MasqueCZ/LuxMeter/blueprints/0.96 I2C display.jpg

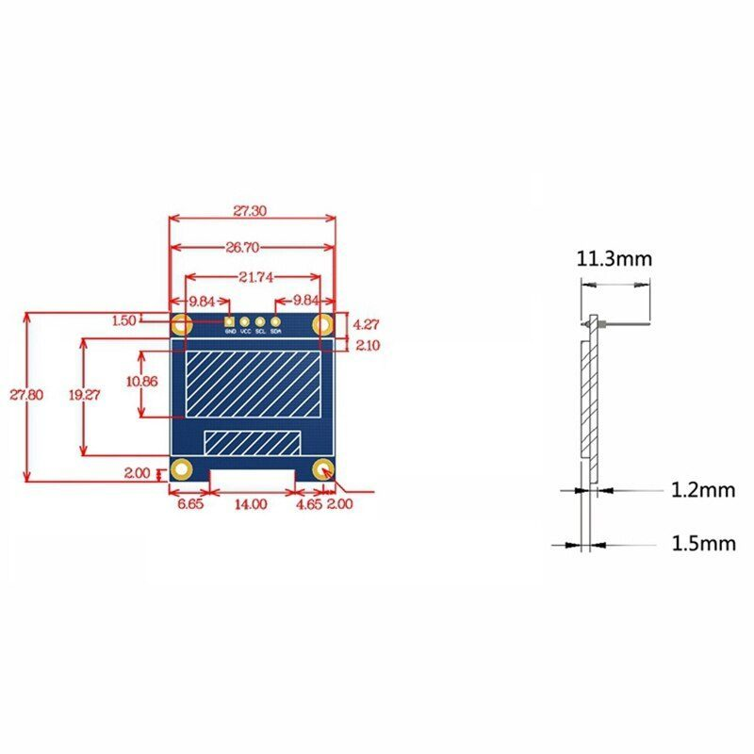
blueprints/0.96 I2C display.jpg
