MasqueCZ/LuxMeter/blueprints/1.54 SPI DISPLAY.jpg

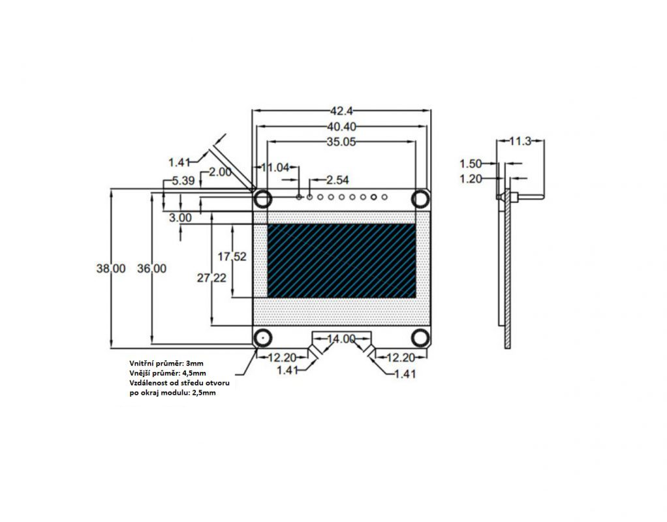
blueprints/1.54 SPI DISPLAY.jpg
