MasqueCZ/LuxMeter/blueprints/CORRIDOR BOX scheme.png

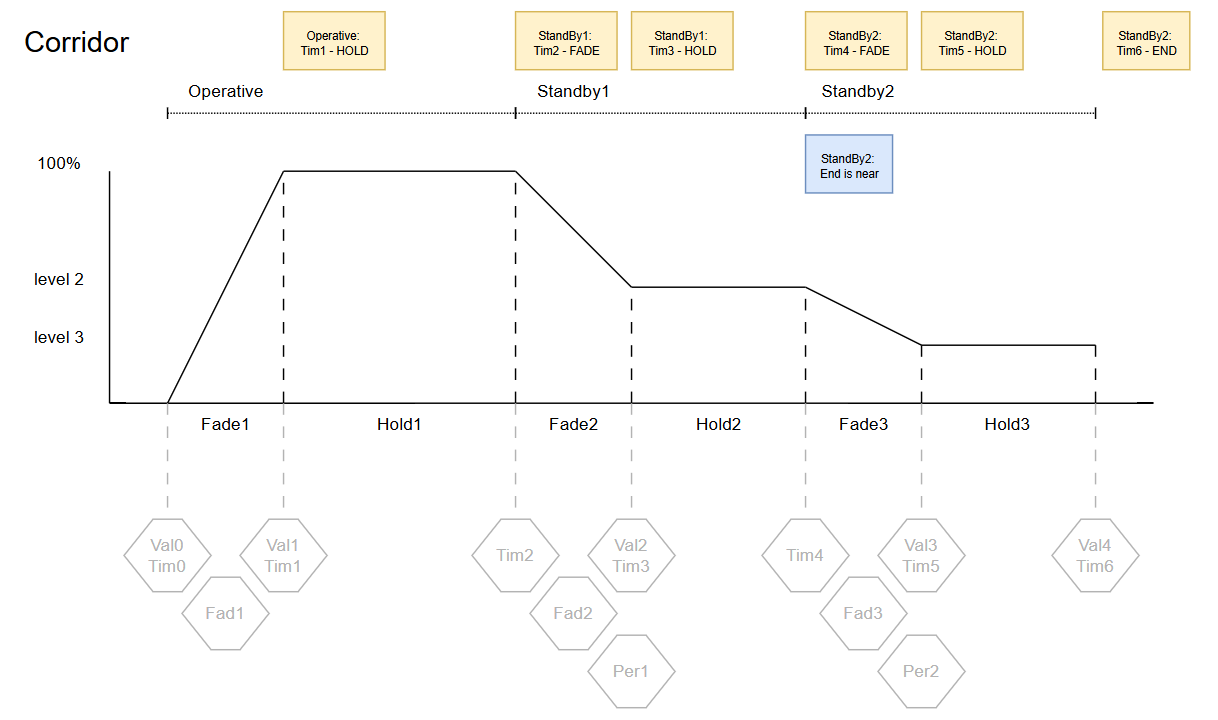
blueprints/CORRIDOR BOX scheme.png
