MasqueCZ/LuxMeter/blueprints/corridor scheme 03.png

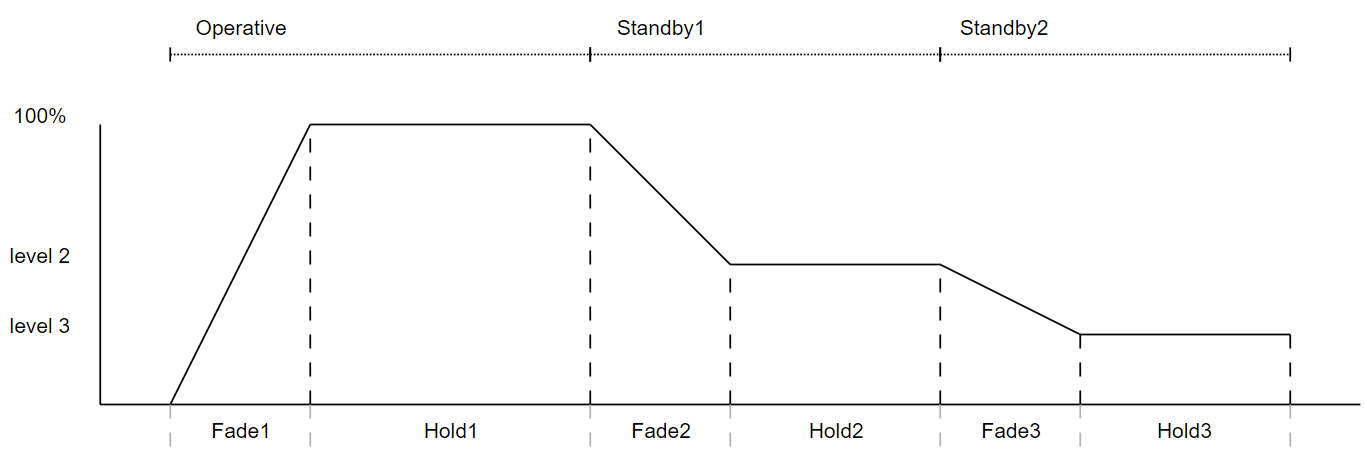
blueprints/corridor scheme 03.png
