MasqueCZ/LuxMeter/blueprints/scheme.jpg

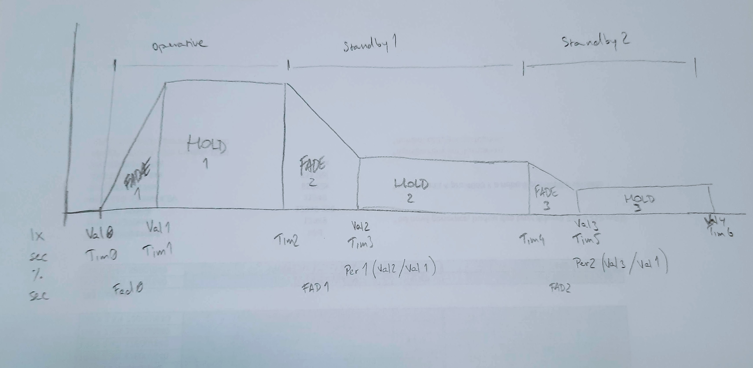
blueprints/scheme.jpg
