MasqueCZ/LuxMeter/HELPMEfile - MANUAL/corr nahled.jpg

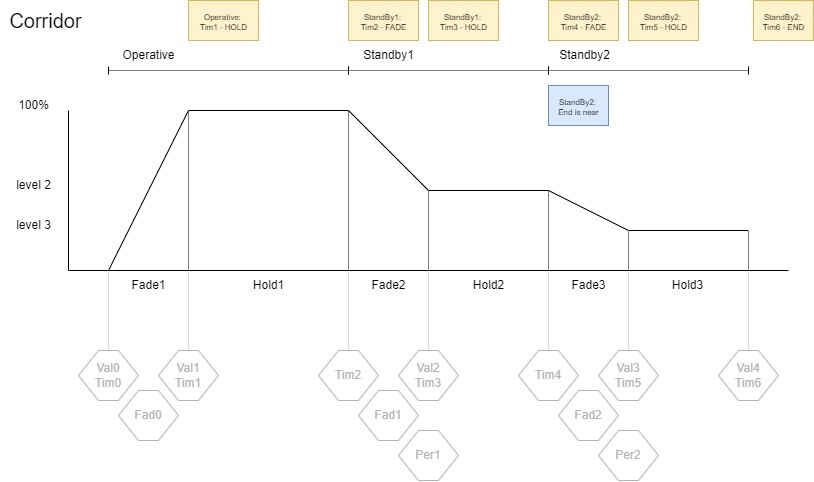
HELPMEfile - MANUAL/corr nahled.jpg
