MasqueCZ/LuxMeter/HELPMEfile - MANUAL/edited/20230224_141636.jpg

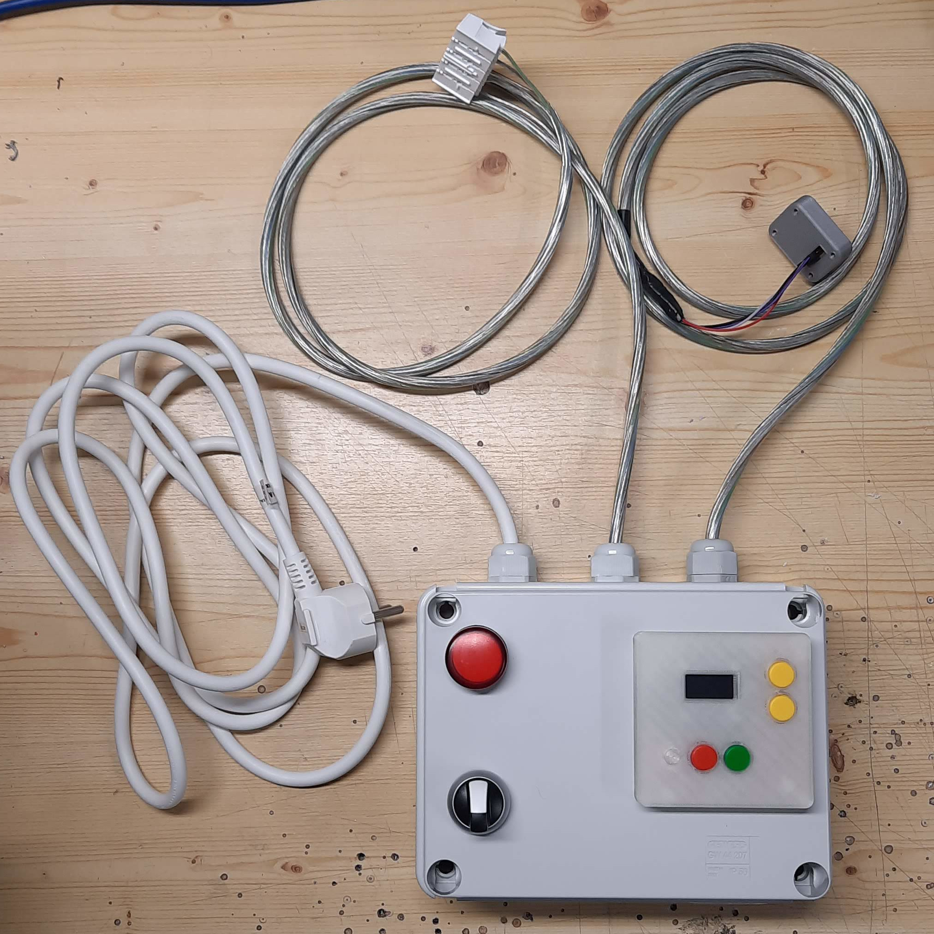
HELPMEfile - MANUAL/edited/20230224_141636.jpg
