MasqueCZ/LuxMeter/HELPMEfile - MANUAL/edited/20230224_143001.jpg

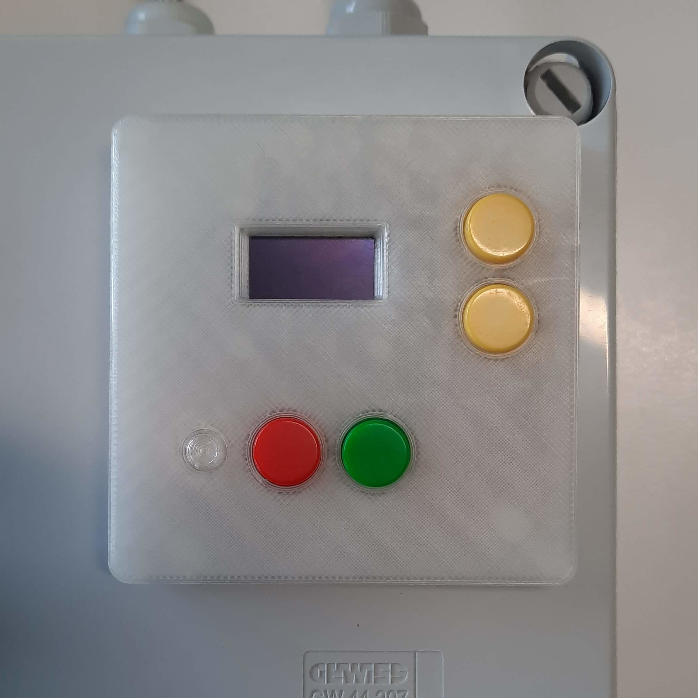
HELPMEfile - MANUAL/edited/20230224_143001.jpg
