MasqueCZ/LuxMeter/HELPMEfile - MANUAL/edited/20230224_143114.jpg

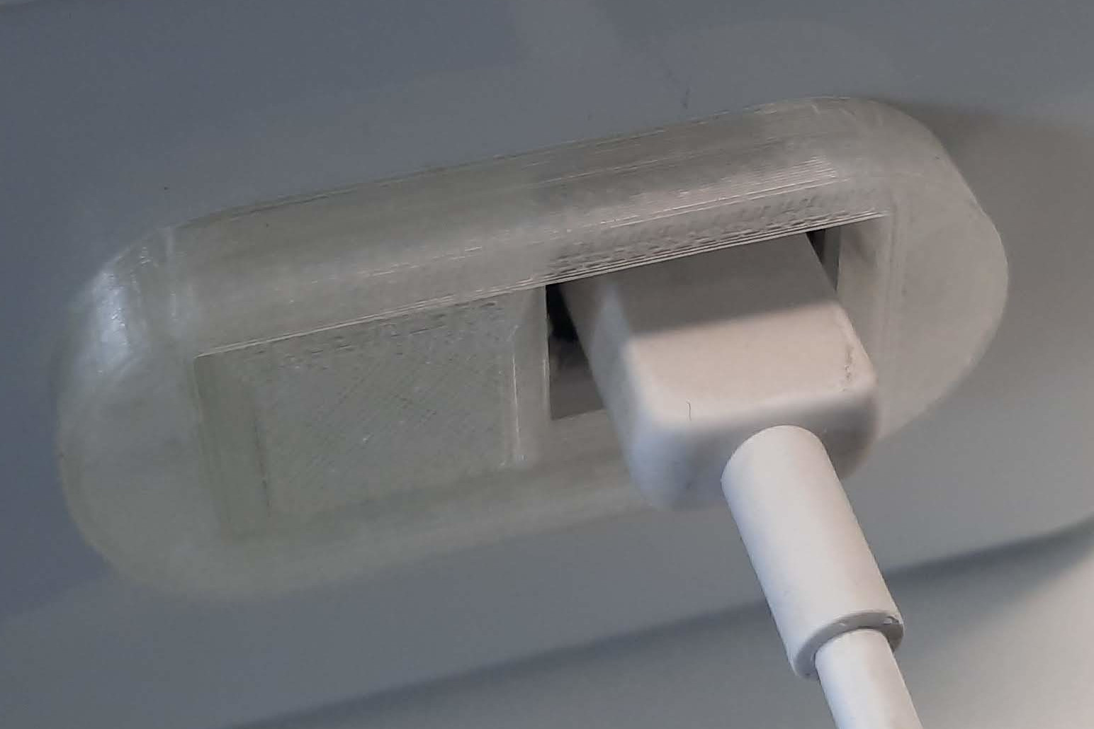
HELPMEfile - MANUAL/edited/20230224_143114.jpg
