MasqueCZ/LuxMeter/HELPMEfile - MANUAL/edited/20230301_140056.jpg

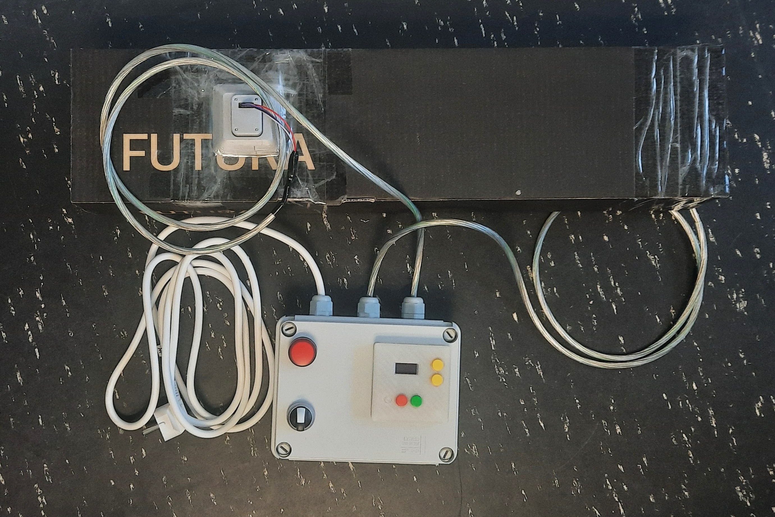
HELPMEfile - MANUAL/edited/20230301_140056.jpg
