MasqueCZ/LuxMeter/HELPMEfile - MANUAL/edited/20240103_172350alpha.jpg

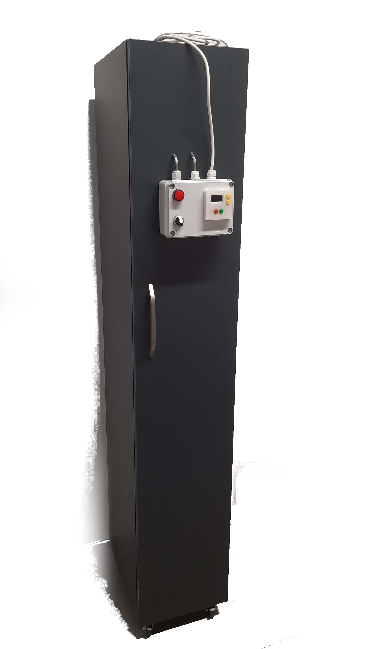
HELPMEfile - MANUAL/edited/20240103_172350alpha.jpg
