MasqueCZ/LuxMeter/HELPMEfile - MANUAL/edited/20240103_172402.jpg

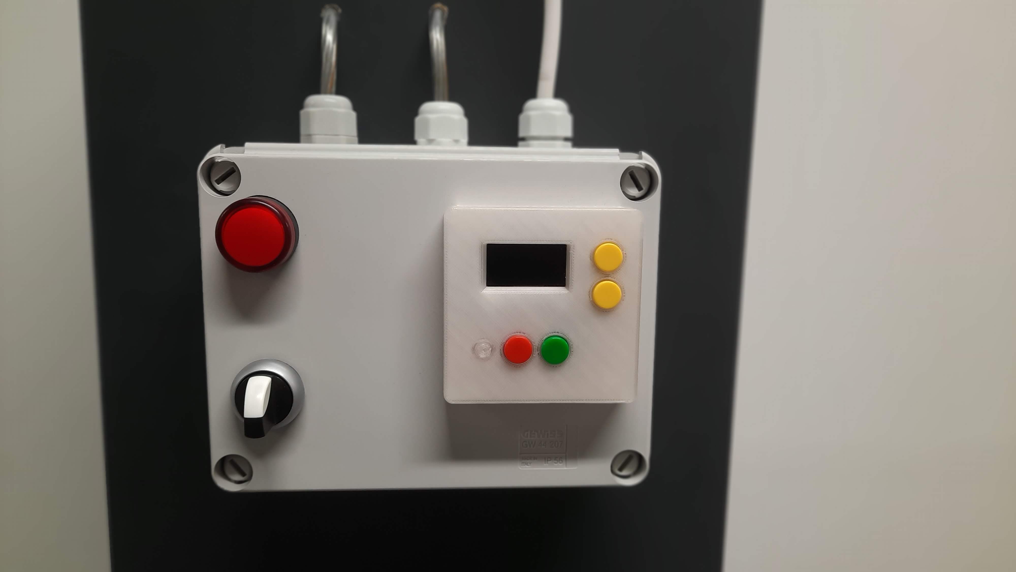
HELPMEfile - MANUAL/edited/20240103_172402.jpg
