MasqueCZ/LuxMeter/HELPMEfile - MANUAL/edited/20240214_140807.jpg

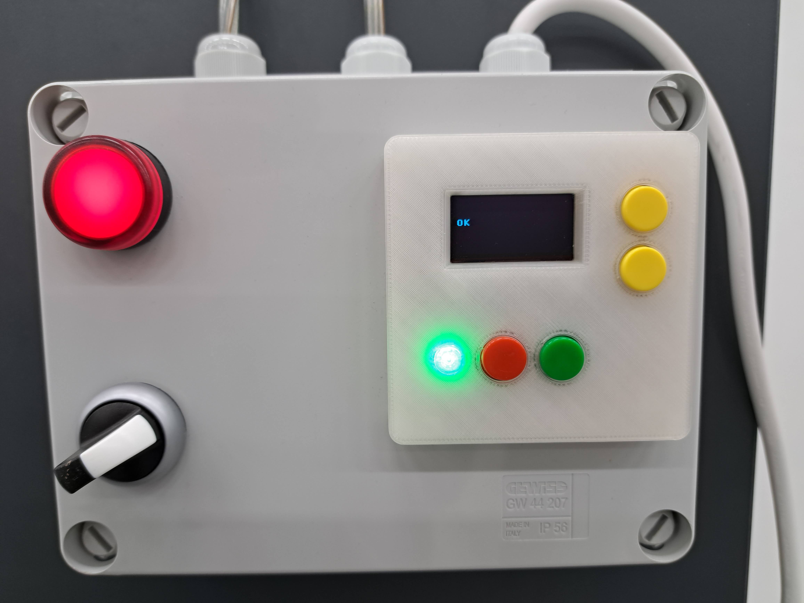
HELPMEfile - MANUAL/edited/20240214_140807.jpg
