MasqueCZ/LuxMeter/HELPMEfile - MANUAL/edited/20240215_122558a.jpg

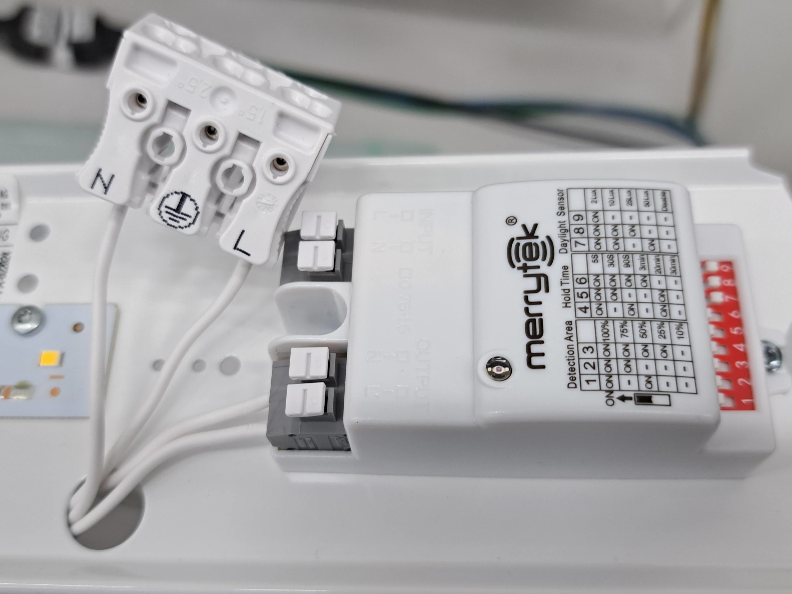
HELPMEfile - MANUAL/edited/20240215_122558a.jpg
