MasqueCZ/LuxMeter/HELPMEfile - MANUAL/edited/jednotka01.jpg

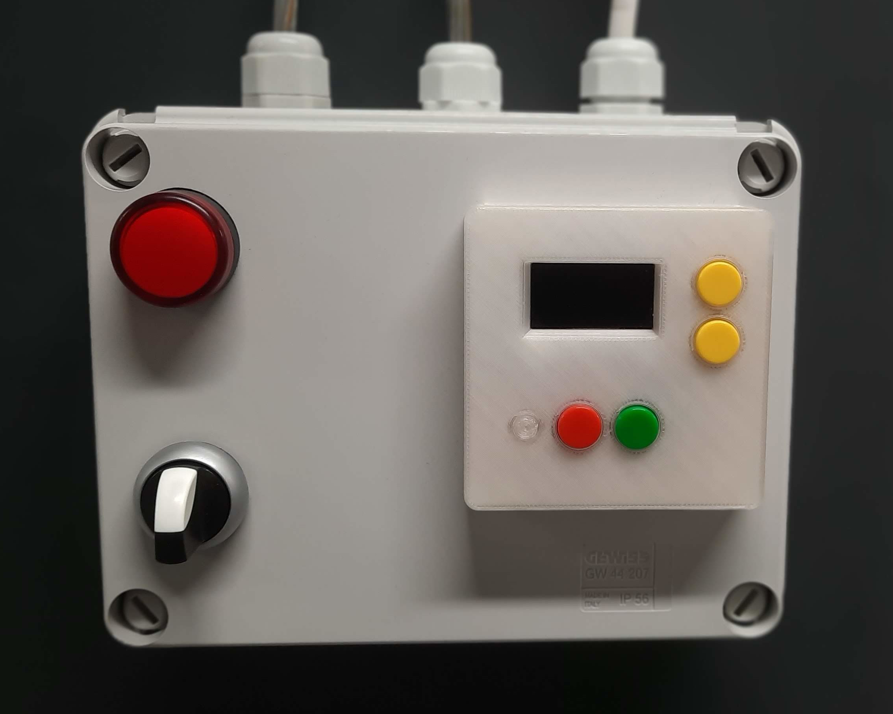
HELPMEfile - MANUAL/edited/jednotka01.jpg
