MasqueCZ/LuxMeter/HELPMEfile - MANUAL/edited/jednotka01alpha.jpg

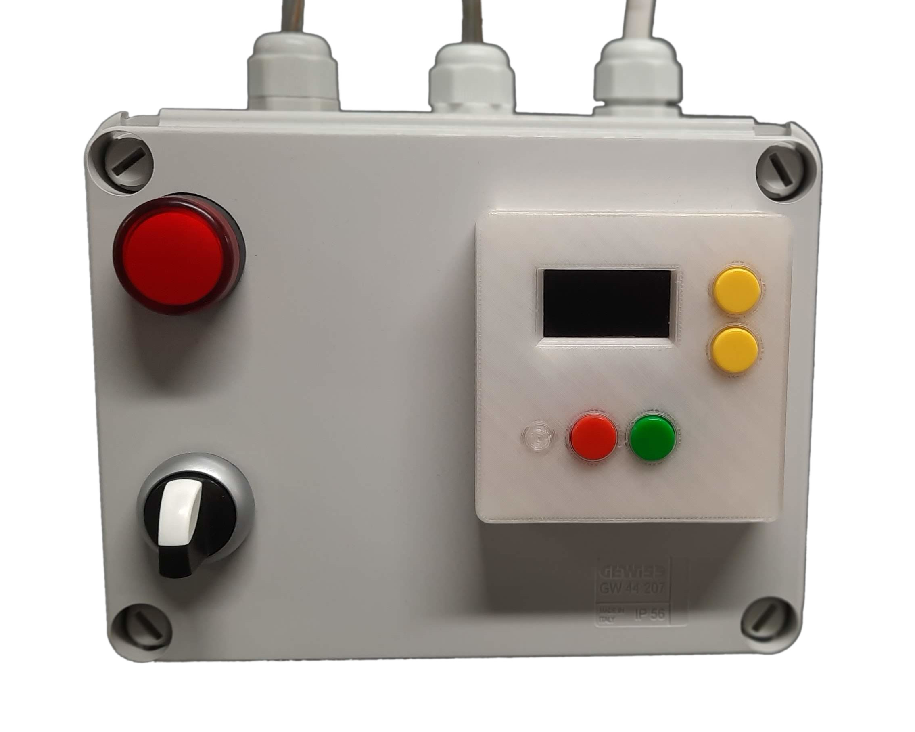
HELPMEfile - MANUAL/edited/jednotka01alpha.jpg
