MasqueCZ/LuxMeter/HELPMEfile - MANUAL/edited/presun.jpg

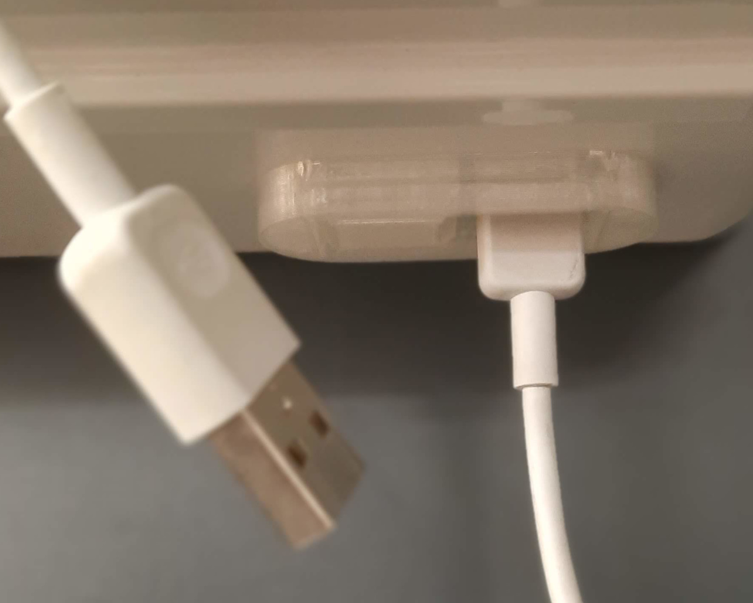
HELPMEfile - MANUAL/edited/presun.jpg
