MasqueCZ/LuxMeter/HELPMEfile - MANUAL/edited/Thonny 00.png

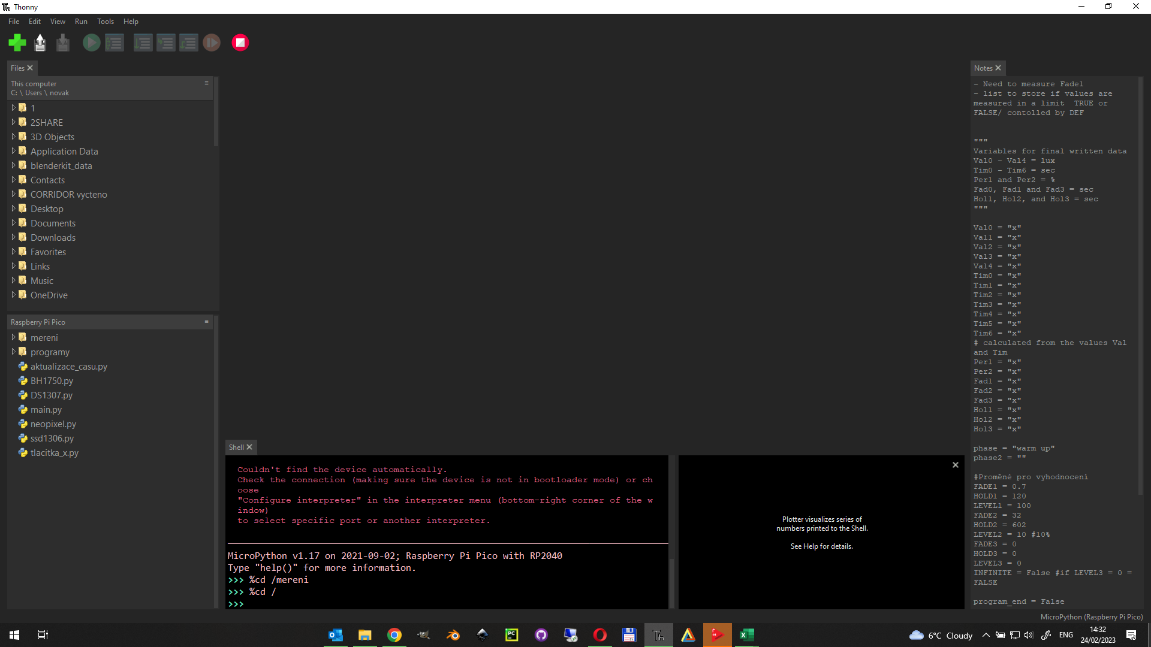
HELPMEfile - MANUAL/edited/Thonny 00.png
