MasqueCZ/LuxMeter/HELPMEfile - MANUAL/edited/Thonny 00inverted.png

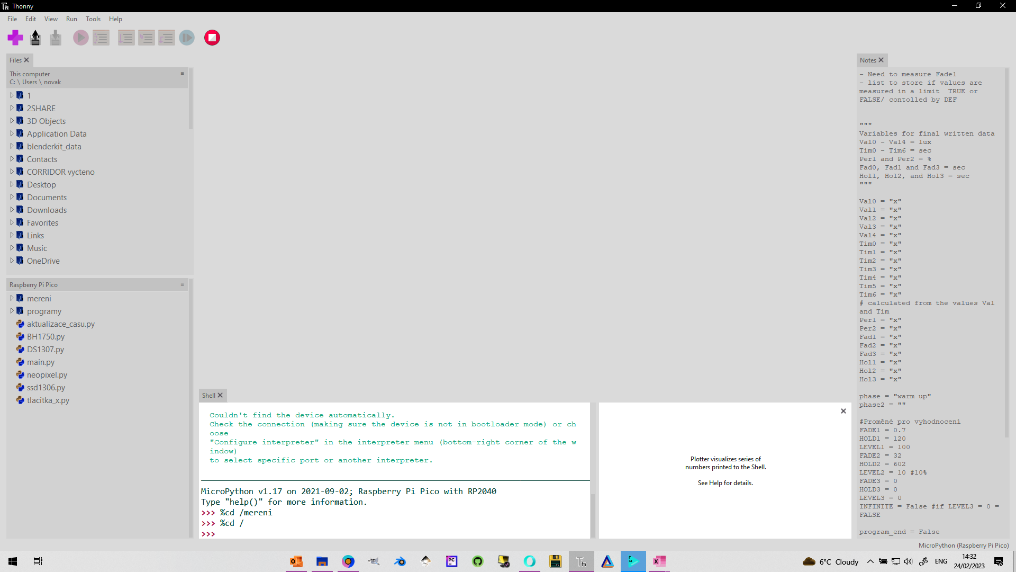
HELPMEfile - MANUAL/edited/Thonny 00inverted.png
