MasqueCZ/LuxMeter/HELPMEfile - MANUAL/edited/Thonny 01.png

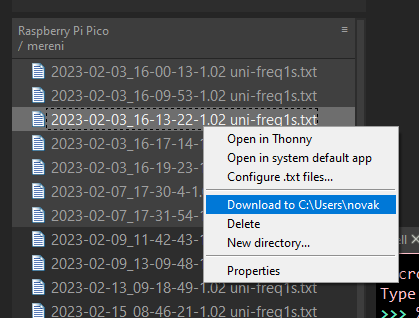
HELPMEfile - MANUAL/edited/Thonny 01.png
