MasqueCZ/LuxMeter/HELPMEfile - MANUAL/edited/Thonny 01inverted.png

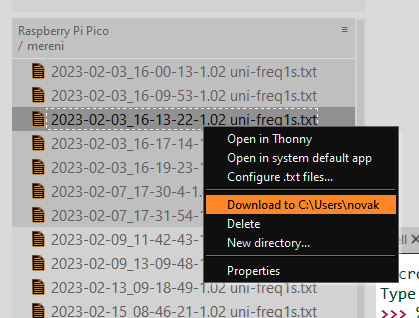
HELPMEfile - MANUAL/edited/Thonny 01inverted.png
