MasqueCZ/LuxMeter/HELPMEfile - MANUAL/Fotky/20230224_141636.jpg

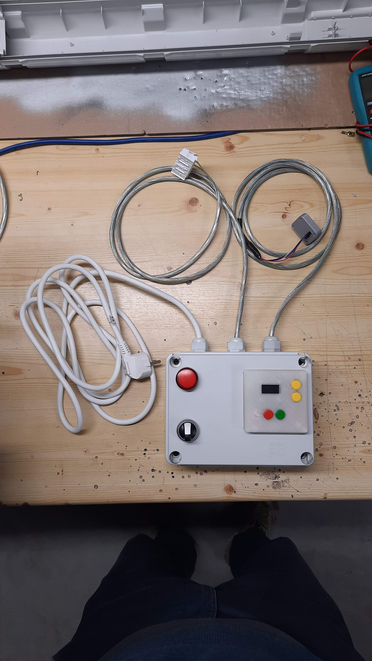
HELPMEfile - MANUAL/Fotky/20230224_141636.jpg
