MasqueCZ/LuxMeter/HELPMEfile - MANUAL/Fotky/20230224_141935.jpg

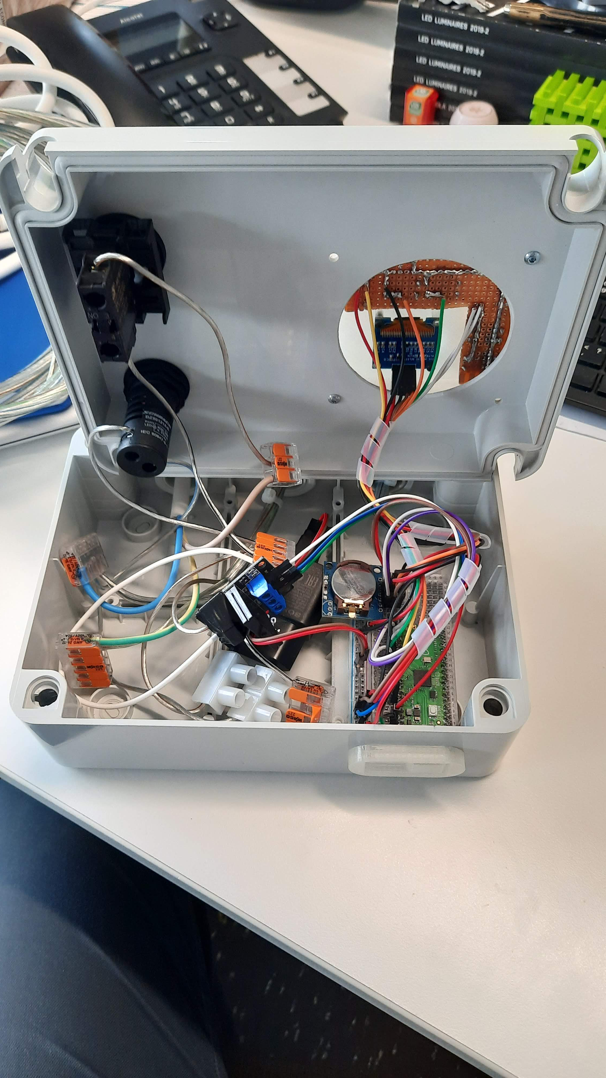
HELPMEfile - MANUAL/Fotky/20230224_141935.jpg
