MasqueCZ/LuxMeter/HELPMEfile - MANUAL/Fotky/20230224_143001.jpg

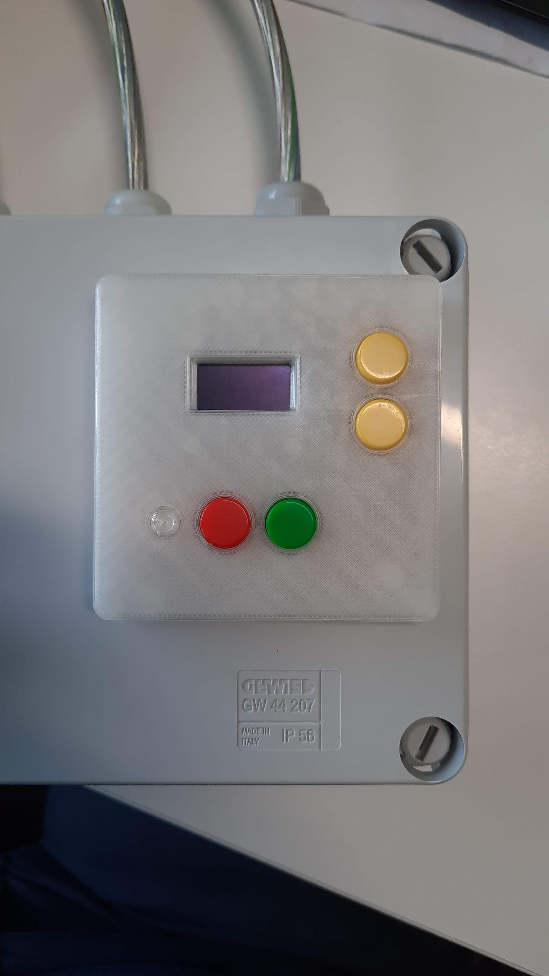
HELPMEfile - MANUAL/Fotky/20230224_143001.jpg
