MasqueCZ/LuxMeter/HELPMEfile - MANUAL/Fotky/20230224_143114.jpg

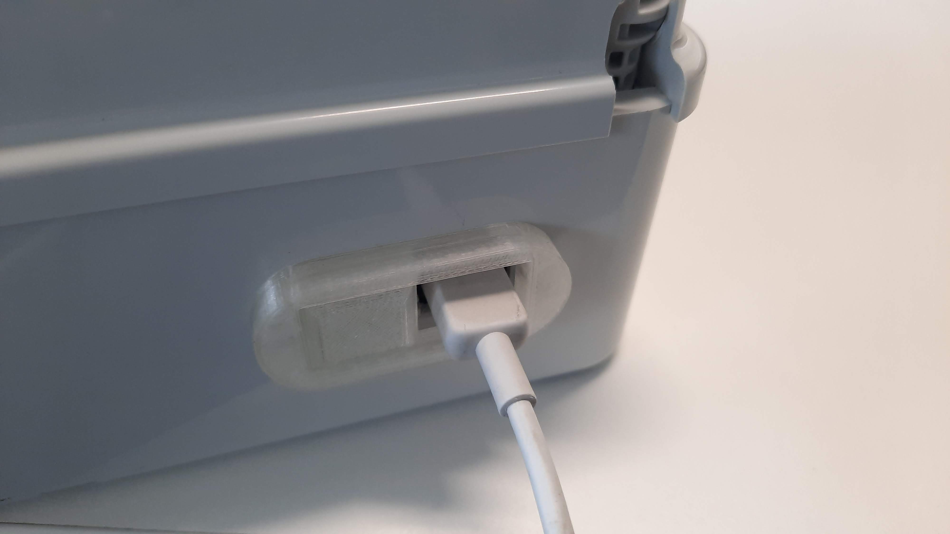
HELPMEfile - MANUAL/Fotky/20230224_143114.jpg
