MasqueCZ/LuxMeter/HELPMEfile - MANUAL/Fotky/20230224_143329.jpg

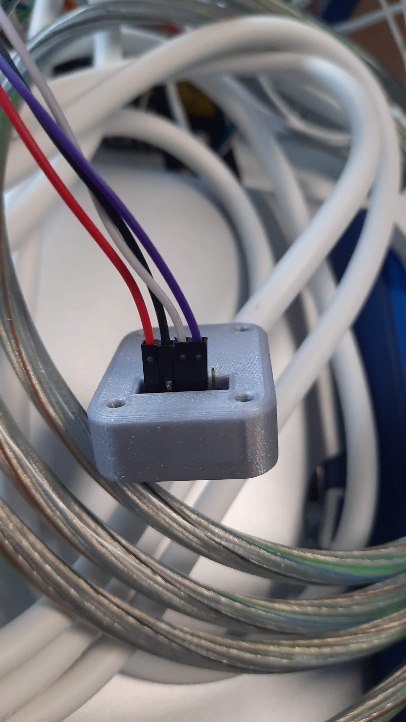
HELPMEfile - MANUAL/Fotky/20230224_143329.jpg
