MasqueCZ/LuxMeter/HELPMEfile - MANUAL/Fotky/20230224_143339.jpg

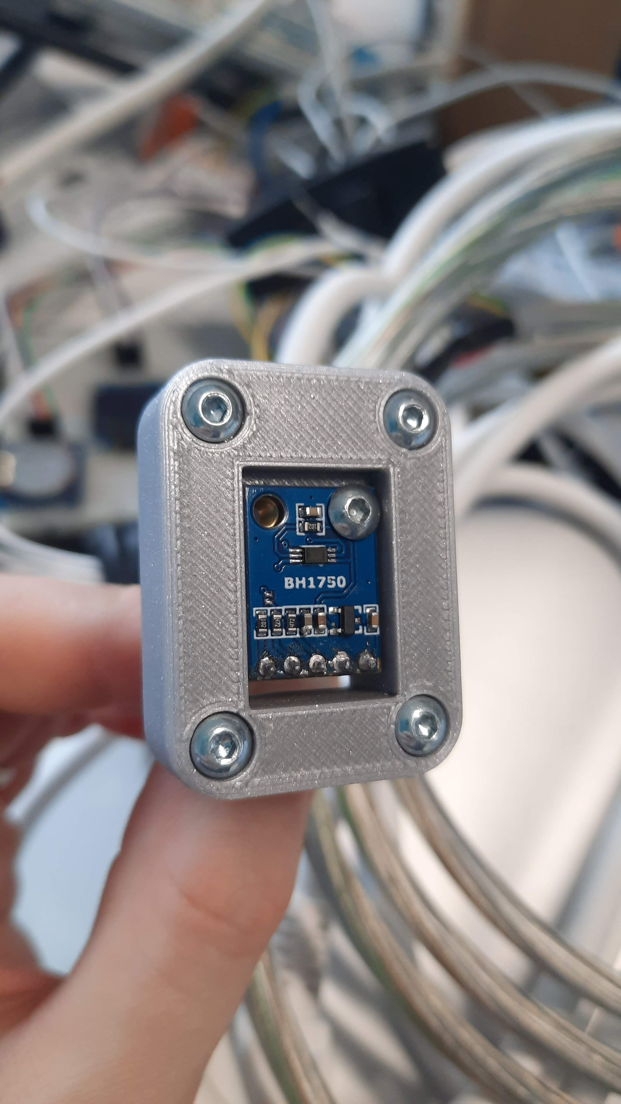
HELPMEfile - MANUAL/Fotky/20230224_143339.jpg
