MasqueCZ/LuxMeter/HELPMEfile - MANUAL/Fotky/20240103_172326.jpg

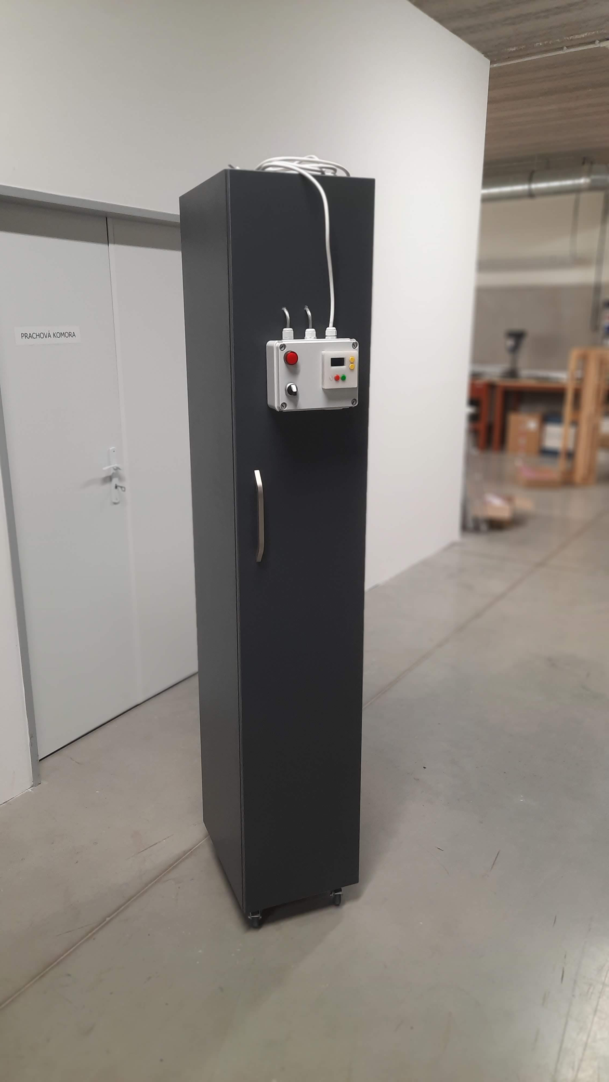
HELPMEfile - MANUAL/Fotky/20240103_172326.jpg
