MasqueCZ/LuxMeter/HELPMEfile - MANUAL/Fotky/20240103_172510alpha.jpg

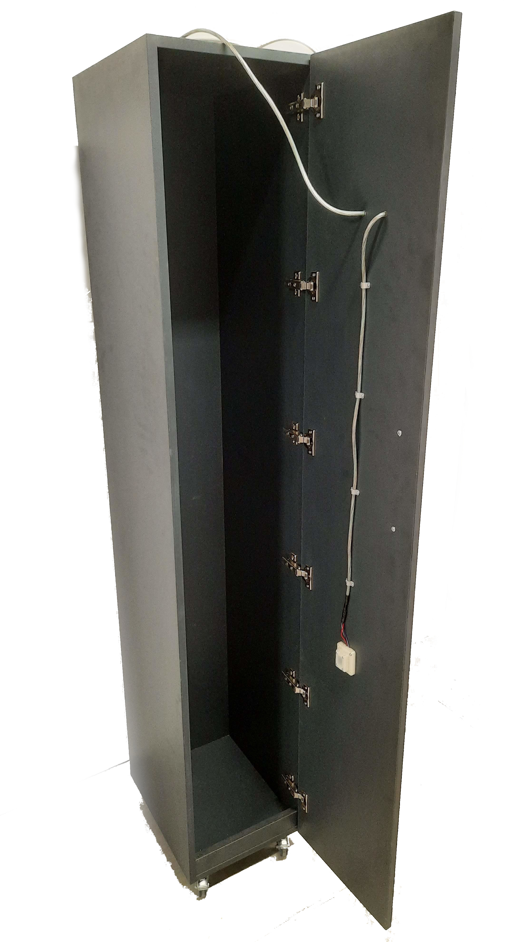
HELPMEfile - MANUAL/Fotky/20240103_172510alpha.jpg
