MasqueCZ/LuxMeter/HELPMEfile - MANUAL/Fotky/20240103_175333.jpg

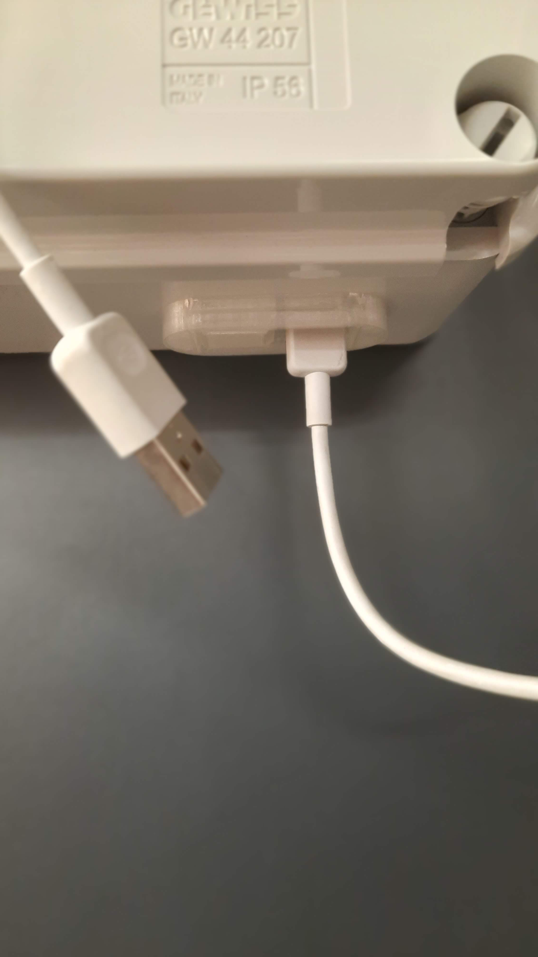
HELPMEfile - MANUAL/Fotky/20240103_175333.jpg
