MasqueCZ/LuxMeter/HELPMEfile - MANUAL/Fotky/20240103_175347.jpg

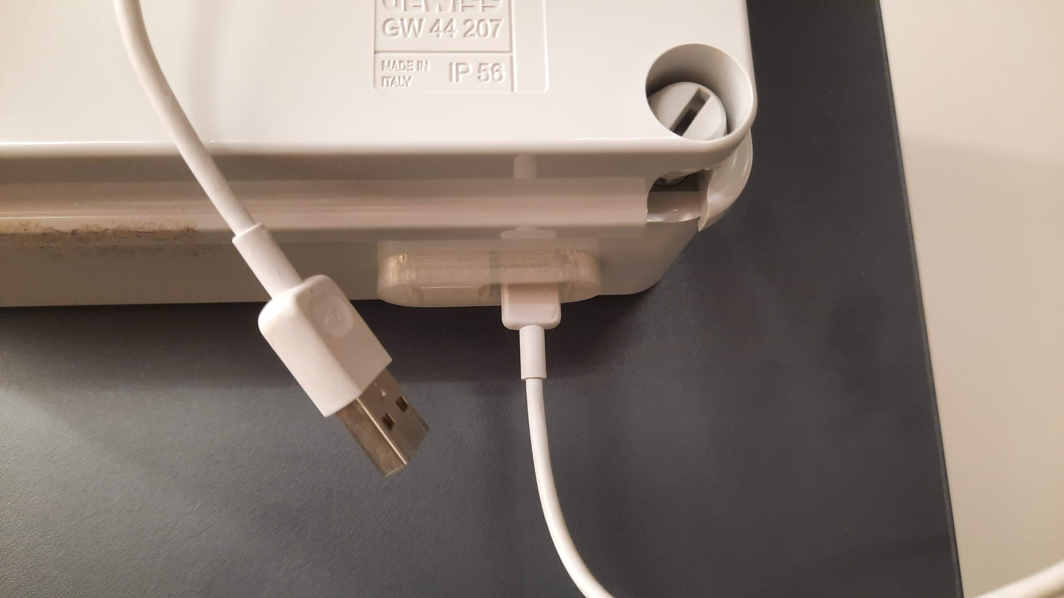
HELPMEfile - MANUAL/Fotky/20240103_175347.jpg
