MasqueCZ/LuxMeter/HELPMEfile - MANUAL/Fotky/20240214_140750.jpg

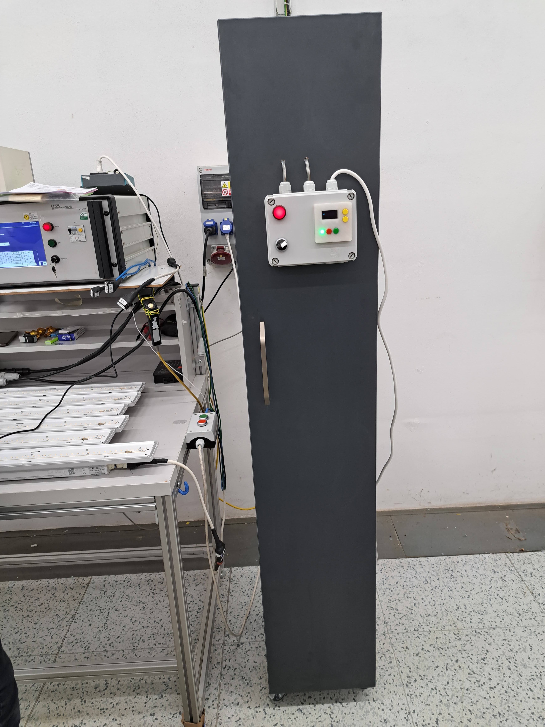
HELPMEfile - MANUAL/Fotky/20240214_140750.jpg
