MasqueCZ/LuxMeter/HELPMEfile - MANUAL/Fotky/20240215_122516.jpg

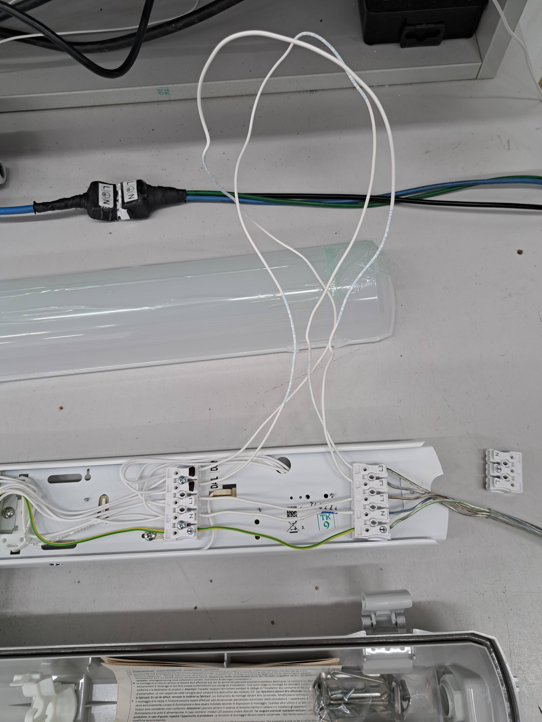
HELPMEfile - MANUAL/Fotky/20240215_122516.jpg
