MasqueCZ/LuxMeter/KiCad_files/new project/new project.kicad_sch

## KiCad design KiCad_files/new project/new project.kicad_sch (2024-04-22)

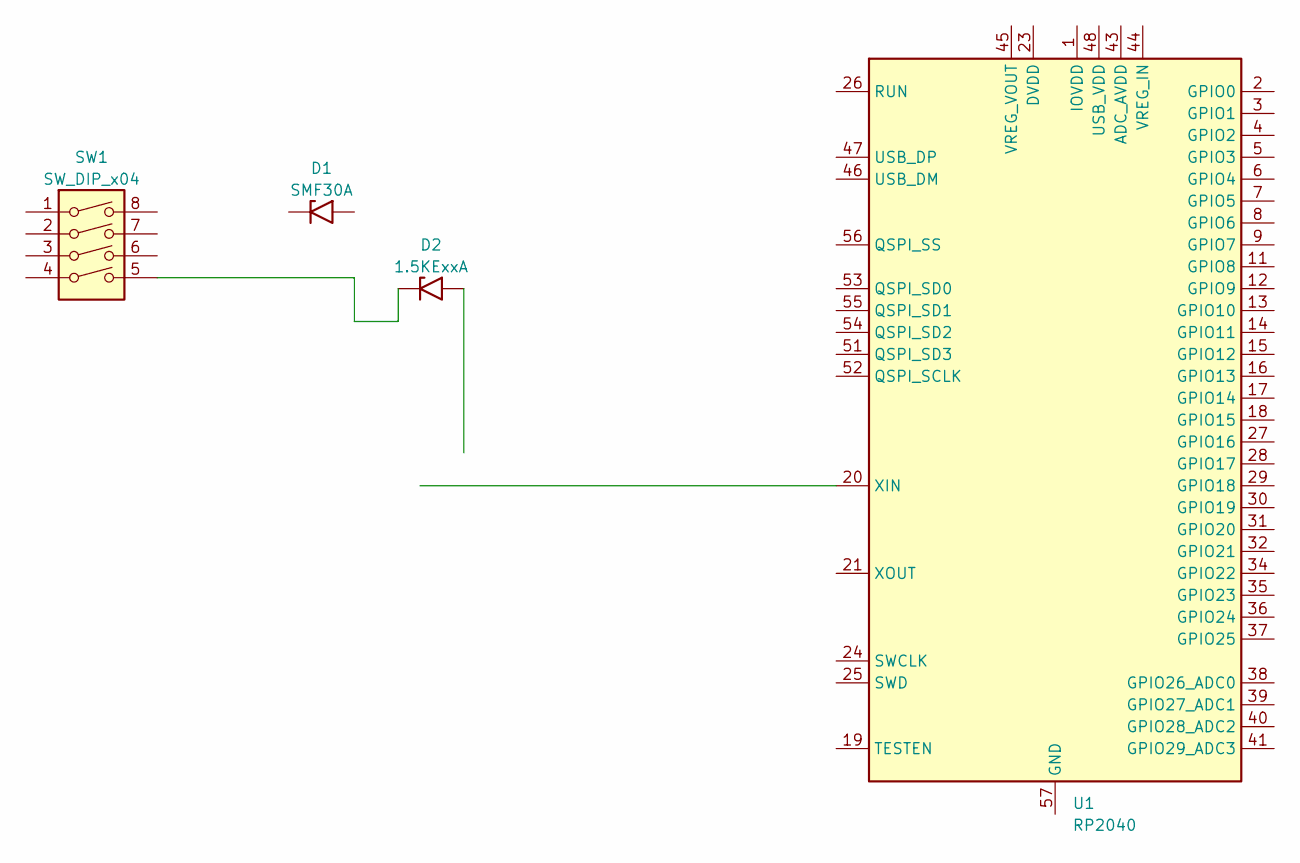
[picture p64: schematic new project.kicad_sch]

Parts:
D1: SMF30A; D_SMF
D2: 1.5KExxA; D_DO-201AE_P15.24mm_Horizontal
SW1: SW_DIP_x04
U1: RP2040; QFN-56-1EP_7x7mm_P0.4mm_EP3.2x3.2mm

Connections:
unnamed: D2.1 (A1), SW1.5
unnamed: U1.1 (IOVDD), U1.10 (IOVDD), U1.22 (IOVDD), U1.33 (IOVDD), U1.42 (IOVDD), U1.49 (IOVDD)
unnamed: U1.23 (DVDD), U1.50 (DVDD)
