MasqueCZ/LuxMeter/KiCad_files/new project/new project/new project.kicad_sch

## KiCad design KiCad_files/new project/new project/new project.kicad_sch (2024-04-22)

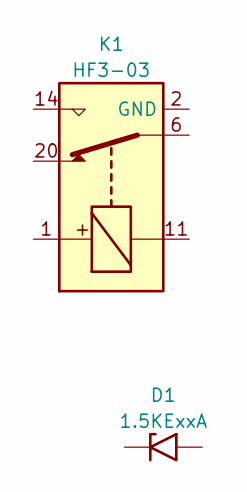
[picture p65: schematic new project.kicad_sch]

Parts:
D1: 1.5KExxA; D_DO-201AE_P15.24mm_Horizontal
K1: HF3-03; Relay_SPDT_AXICOM_HF3Series_75ohms_Pitch1.27mm

Connections:
unnamed: K1.2 (GND), K1.5 (GND), K1.7 (GND), K1.10 (GND), K1.12 (GND), K1.13 (GND), K1.15 (GND), K1.17 (GND), K1.19 (GND), K1.21 (GND), K1.22 (GND)
