MasqueCZ/LuxMeter/main.py

# built on Rotary Menu
# by Kevin McAleer
# May 2021
# edited by Michal Novak June 2022

from machine import Pin, I2C
from os import listdir
from SH1106 import SH1106_I2C
from utime import sleep
from BH1750 import BH1750
from neopixel import Neopixel
import DS1307, _thread, micropython
import config

DEBUG = False
print(f"box # {config.box_version}")
print(f"version {config.v}")
rotate_display = config.display_rotation

# I2C variables
i2c = I2C(0, scl=Pin(17), sda=Pin(16), freq=400000)

# Screen Variables
width = 128
height = 64
line = 1
highlight = 1
shift = 0
list_length = 0
total_lines = 6



# create the display
oled = SH1106_I2C(width=width, height=height, i2c=i2c, rotate=rotate_display)
oled.fill(0)
oled.init_display()

# Setup the Rotary Encoder - OK - UP - DOWN
button_ok = Pin(20, Pin.IN, Pin.PULL_DOWN)
button_up = Pin(19, Pin.IN, Pin.PULL_DOWN)
button_do = Pin(18, Pin.IN, Pin.PULL_DOWN)

# relays
relay = Pin(21, Pin.OUT)
relay02 = Pin(22, Pin.OUT)
relay.value(1)
relay02.value(1)

# strip of 1 chips, state machine 0, GPIO 28(pin34), RGB mode
n_leds = 1
pixels = Neopixel(n_leds, 0, 28, "GRB")

# re-sets MOOD LED
pixels.fill((0, 0, 0))
pixels.show()


def get_files():
    """ Get a list of Python files in the root folder of the Pico """

    files = listdir("/programs/")
    menu = []
    for file in files:
        if file.endswith(".py"):
            menu.append(file)

    return (menu)


def show_menu(menu):
    """ Shows the menu on the screen"""

    # bring in the global variables
    global line, highlight, shift, list_length

    # menu variables
    item = 1
    line = 1
    line_height = 10

    # clear the display
    oled.fill_rect(0, 0, width, height, 0)

    # Shift the list of files so that it shows on the display
    list_length = len(menu)
    short_list = menu[shift:shift + total_lines]

    for item in short_list:
        if highlight == line:
            oled.fill_rect(0, (line - 1) * line_height, width, line_height, 1)
            oled.text(">", 0, (line - 1) * line_height, 0)
            oled.text(item, 10, (line - 1) * line_height, 0)
            oled.show()
        else:
            oled.text(item, 10, (line - 1) * line_height, 1)
            oled.show()
        line += 1
    oled.show()


def launch(filename):
    """ Launch the Python script <filename> """
    global file_list
    # clear the screen
    oled.fill_rect(0, 0, width, height, 0)
    oled.text("Launching", 1, 10)
    oled.text(filename, 1, 20)
    oled.show()
    sleep(0.5)
    progloc = ("/programs/"+filename)
    exec(open(progloc).read())
    show_menu(file_list)


# Get the list of Python files and display the menu
file_list = get_files()
show_menu(file_list)

# Repeat forever
while True:
    if button_up.value() == True:
        if highlight > 1:
            highlight -= 1
            if DEBUG == True:
                print("up.highlight")
            sleep(0.1)
            show_menu(file_list)
        else:
            if shift > 0:
                shift -= 1
                if DEBUG == True:
                    print("up.shift")
                sleep(0.1)
                show_menu(file_list)

    if button_do.value() == True:
        if highlight < total_lines:
            highlight += 1
            if DEBUG == True:
                print("down.highlight")
            sleep(0.1)
            show_menu(file_list)
        else:
            if shift + total_lines < list_length:
                shift += 1
                if DEBUG == True:
                    print("down.shift")
                sleep(0.1)
                show_menu(file_list)

    # Check for button pressed
    if button_ok.value() == True:
        if DEBUG == True:
            print("Launching", file_list[highlight - 1 + shift])

            # execute script
        launch(file_list[(highlight - 1) + shift])
        if DEBUG == True:
            print("Returned from launch")
    pixels.fill((0,0,0))
    pixels.show()
