MasqueCZ/LuxMeter/images/SPI test.py

"""SSD1309 demo (shapes)."""
from time import sleep
from machine import Pin, SPI
from ssd1309 import Display

from utime import sleep_us, ticks_us, ticks_diff

led = Pin('LED', machine.Pin.OUT)

led.on()

def test():
    """Test code.
    SCK=SCL
    MOSI=SDA
    rst=RES
    dc=DC
    cs=CS"""
    spi = SPI(1, baudrate=10000000, sck=Pin(10), mosi=Pin(11))
    display = Display(spi, dc=Pin(4), cs=Pin(5), rst=Pin(2))

    display.draw_rectangle(1, 1, 30, 30)
    display.fill_rectangle(6, 6, 20,20)

    display.fill_circle(50, 16, 14)
    display.draw_circle(50, 16, 10, invert=True)

    coords = [[106, 0], [106, 60], [70, 11], [127, 30], [70, 49], [106, 0]]
    display.draw_lines(coords)

    display.fill_ellipse(16, 48, 15, 8)
    display.draw_ellipse(16, 48, 8, 15)

    display.fill_polygon(5, 50, 48, 8)
    display.draw_polygon(7, 50, 48, 15)

    display.draw_line(117, 63, 127, 53)
    display.draw_vline(127, 53, 10)
    display.draw_hline(117, 63, 10)

    display.present()

    sleep(10)
    display.cleanup()
    print('Done.')


test()
led.off()

class BouncingSprite(object):
    """Bouncing Sprite."""

    def __init__(self, path, w, h, screen_width, screen_height,
                 speed, display):
        """Initialize sprite.
        Args:
            path (string): Path of sprite image.
            w, h (int): Width and height of image.
            screen_width (int): Width of screen.
            screen_height (int): Width of height.
            size (int): Square side length.
            speed(int): Initial XY-Speed of sprite.
            display (SSD1351): OLED display object.
            color (int): RGB565 color value.
        """
        self.buf = display.load_sprite(path, w, h, invert=True)
        self.w = w
        self.h = h
        self.screen_width = screen_width
        self.screen_height = screen_height
        self.display = display
        self.x_speed = speed
        self.y_speed = speed
        self.x = self.screen_width // 2
        self.y = self.screen_height // 2
        self.prev_x = self.x
        self.prev_y = self.y

    def update_pos(self):
        """Update sprite speed and position."""
        x = self.x
        y = self.y
        w = self.w
        h = self.h
        x_speed = abs(self.x_speed)
        y_speed = abs(self.y_speed)

        if x + w + x_speed >= self.screen_width:
            self.x_speed = -x_speed
        elif x - x_speed < 0:
            self.x_speed = x_speed

        if y + h + y_speed >= self.screen_height:
            self.y_speed = -y_speed
        elif y - y_speed <= 0:
            self.y_speed = y_speed

        self.prev_x = x
        self.prev_y = y

        self.x = x + self.x_speed
        self.y = y + self.y_speed

    def draw(self):
        """Draw sprite."""
        x = self.x
        y = self.y
        prev_x = self.prev_x
        prev_y = self.prev_y
        w = self.w
        h = self.h
        x_speed = abs(self.x_speed)
        y_speed = abs(self.y_speed)

        # Determine direction and remove previous portion of sprite
        if prev_x > x:
            # Left
            self.display.fill_rectangle(x + w, prev_y, x_speed, h, invert=True)
        elif prev_x < x:
            # Right
            self.display.fill_rectangle(x - x_speed, prev_y, x_speed, h, invert=True)
        if prev_y > y:
            # Upward
            self.display.fill_rectangle(prev_x, y + h, w, y_speed, invert=True)
        elif prev_y < y:
            # Downward
            self.display.fill_rectangle(prev_x, y - y_speed, w, y_speed, invert=True)

        self.display.draw_sprite(self.buf, x, y, w, h)
        self.display.present()


def test2():
    """Bouncing sprite."""
    try:
        # Baud rate of 14500000 seems about the max
        spi = SPI(1, baudrate=10000000, sck=Pin(10), mosi=Pin(11))
        display = Display(spi, dc=Pin(4), cs=Pin(5), rst=Pin(2))
        display.clear()

        # Load sprite
        saucer = BouncingSprite('images/saucer_48x26.mono',
                              48, 26, 128, 64, 1, display)

        while True:
            timer = ticks_us()
            saucer.update_pos()
            saucer.draw()
            # Attempt to set framerate to 30 FPS
            timer_dif = 33333 - ticks_diff(ticks_us(), timer)
            if timer_dif > 0:
                sleep_us(timer_dif)

    except KeyboardInterrupt:
        display.cleanup()


test2()
