MasqueCZ/LuxMeter/HELPMEfile - MANUAL/Fotky/20240214_141401.jpg

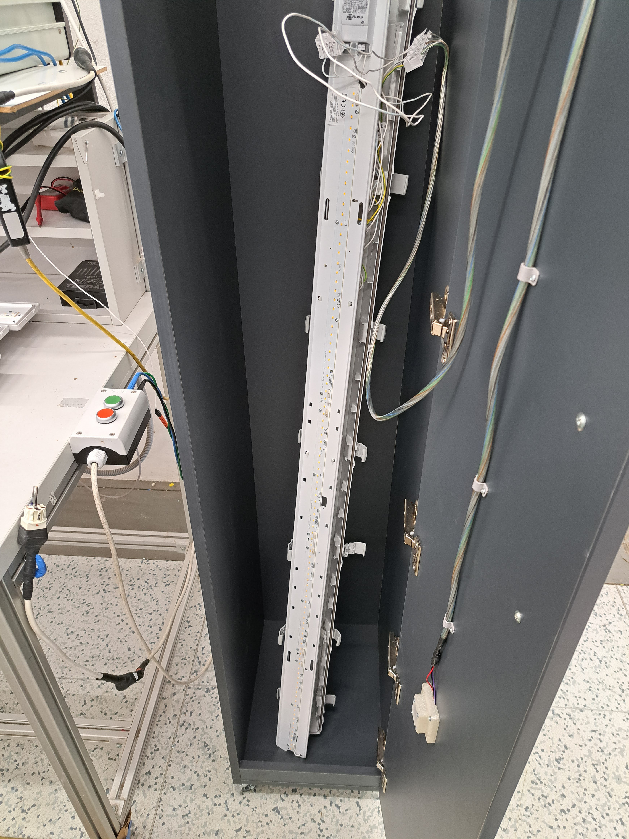
HELPMEfile - MANUAL/Fotky/20240214_141401.jpg
